maciejmatczak/more-organic/data/case/assembly.scad

$fa = 6;
$fs = .1;


union() {
	color(c = [1, 1, 0.8000000000, 0.5000000000]) {
		linear_extrude(height = 1.6000000000) {
			offset(r = -2) {
				offset(r = 2) {
					union() {
						offset(r = -12) {
							offset(r = 16) {
								union() {
									intersection() {
										offset(r = -10) {
											offset(r = 10) {
												translate(v = [-16.2000000000, -42.8000000000]) {
													rotate(a = 180.0000000000) {
														polygon(paths = [[0, 1, 2, 3]], points = [[-1.5000000000, 1.5000000000], [8, 1.5000000000], [8, -6], [-1.5000000000, -6]]);
													}
												}
												translate(v = [-40.0000000000, -2.0000000000]) {
													color(c = [0.3000000000, 0.3000000000, 0.3000000000]) {
														mirror(v = [0, 1, 0]) {
															polygon(paths = [[0, 1, 2, 3, 4, 5, 6, 7]], points = [[-5.3500000000, 12.1000000000], [5.3500000000, 12.1000000000], [5.3500000000, 0], [5.1000000000, 0], [5.1000000000, -2], [-5.1000000000, -2], [-5.1000000000, 0], [-5.3500000000, 0]]);
														}
													}
												}
												translate(v = [-24.0000000000, -17.8000000000]) {
													rotate(a = -90.0000000000) {
														color(c = [0.0040000000, 0.2274509804, 0.5764705882, 0.5000000000]) {
															polygon(paths = [[0, 1, 2, 3]], points = [[-17.8000000000, 8.9000000000], [15.2000000000, 8.9000000000], [15.2000000000, -8.9000000000], [-17.8000000000, -8.9000000000]]);
														}
													}
												}
												translate(v = [-39.8000000000, -21.2000000000]) {
													rotate(a = -90.0000000000) {
														polygon(paths = [[0, 1, 2, 3]], points = [[-4.7000000000, -1.1000000000], [4.7000000000, -1.1000000000], [4.7000000000, 1.1000000000], [-4.7000000000, 1.1000000000]]);
													}
												}
												translate(v = [-43.3000000000, -21.2000000000]) {
													rotate(a = -90.0000000000) {
														polygon(paths = [[0, 1, 2, 3]], points = [[-4.7000000000, -1.1000000000], [4.7000000000, -1.1000000000], [4.7000000000, 1.1000000000], [-4.7000000000, 1.1000000000]]);
													}
												}
												translate(v = [-36.1000000000, -18.6000000000]) {
													rotate(a = 180.0000000000) {
														polygon(paths = [[0, 1, 2, 3]], points = [[-1.6500000000, -1.2400000000], [1.6500000000, -1.2400000000], [1.6500000000, 1.2400000000], [-1.6500000000, 1.2400000000]]);
													}
												}
												translate(v = [-36.1000000000, -24.4000000000]) {
													polygon(paths = [[0, 1, 2, 3]], points = [[-1.6500000000, -1.2400000000], [1.6500000000, -1.2400000000], [1.6500000000, 1.2400000000], [-1.6500000000, 1.2400000000]]);
												}
											}
										}
										translate(v = [0, -4]) {
											offset(r = -10) {
												offset(r = 10) {
													translate(v = [-16.2000000000, -42.8000000000]) {
														rotate(a = 180.0000000000) {
															polygon(paths = [[0, 1, 2, 3]], points = [[-1.5000000000, 1.5000000000], [8, 1.5000000000], [8, -6], [-1.5000000000, -6]]);
														}
													}
													translate(v = [-40.0000000000, -2.0000000000]) {
														color(c = [0.3000000000, 0.3000000000, 0.3000000000]) {
															mirror(v = [0, 1, 0]) {
																polygon(paths = [[0, 1, 2, 3, 4, 5, 6, 7]], points = [[-5.3500000000, 12.1000000000], [5.3500000000, 12.1000000000], [5.3500000000, 0], [5.1000000000, 0], [5.1000000000, -2], [-5.1000000000, -2], [-5.1000000000, 0], [-5.3500000000, 0]]);
															}
														}
													}
													translate(v = [-24.0000000000, -17.8000000000]) {
														rotate(a = -90.0000000000) {
															color(c = [0.0040000000, 0.2274509804, 0.5764705882, 0.5000000000]) {
																polygon(paths = [[0, 1, 2, 3]], points = [[-17.8000000000, 8.9000000000], [15.2000000000, 8.9000000000], [15.2000000000, -8.9000000000], [-17.8000000000, -8.9000000000]]);
															}
														}
													}
													translate(v = [-39.8000000000, -21.2000000000]) {
														rotate(a = -90.0000000000) {
															polygon(paths = [[0, 1, 2, 3]], points = [[-4.7000000000, -1.1000000000], [4.7000000000, -1.1000000000], [4.7000000000, 1.1000000000], [-4.7000000000, 1.1000000000]]);
														}
													}
													translate(v = [-43.3000000000, -21.2000000000]) {
														rotate(a = -90.0000000000) {
															polygon(paths = [[0, 1, 2, 3]], points = [[-4.7000000000, -1.1000000000], [4.7000000000, -1.1000000000], [4.7000000000, 1.1000000000], [-4.7000000000, 1.1000000000]]);
														}
													}
													translate(v = [-36.1000000000, -18.6000000000]) {
														rotate(a = 180.0000000000) {
															polygon(paths = [[0, 1, 2, 3]], points = [[-1.6500000000, -1.2400000000], [1.6500000000, -1.2400000000], [1.6500000000, 1.2400000000], [-1.6500000000, 1.2400000000]]);
														}
													}
													translate(v = [-36.1000000000, -24.4000000000]) {
														polygon(paths = [[0, 1, 2, 3]], points = [[-1.6500000000, -1.2400000000], [1.6500000000, -1.2400000000], [1.6500000000, 1.2400000000], [-1.6500000000, 1.2400000000]]);
													}
												}
											}
										}
									}
									translate(v = [13.4000000000, -78.5000000000]) {
										rotate(a = -6.6000000000) {
											translate(v = [-7.8000000000, -7.0000000000]) {
												polygon(paths = [[0, 1, 2, 3, 4, 5, 6, 7, 8, 9, 10, 11, 12, 13, 14, 15, 16, 17, 18, 19]], points = [[0.8000000000, 0], [14.8000000000, 0], [14.8000000000, 1], [15.6000000000, 1], [15.6000000000, 4.5000000000], [14.8000000000, 4.5000000000], [14.8000000000, 9.5000000000], [15.6000000000, 9.5000000000], [15.6000000000, 13], [14.8000000000, 13], [14.8000000000, 14], [0.8000000000, 14], [0.8000000000, 13], [0, 13], [0, 9.5000000000], [0.8000000000, 9.5000000000], [0.8000000000, 4.5000000000], [0, 4.5000000000], [0, 1], [0.8000000000, 1]]);
											}
										}
									}
									translate(v = [-9.3000000000, -79.9000000000]) {
										rotate(a = 18.0000000000) {
											translate(v = [-7.8000000000, -7.0000000000]) {
												polygon(paths = [[0, 1, 2, 3, 4, 5, 6, 7, 8, 9, 10, 11, 12, 13, 14, 15, 16, 17, 18, 19]], points = [[0.8000000000, 0], [14.8000000000, 0], [14.8000000000, 1], [15.6000000000, 1], [15.6000000000, 4.5000000000], [14.8000000000, 4.5000000000], [14.8000000000, 9.5000000000], [15.6000000000, 9.5000000000], [15.6000000000, 13], [14.8000000000, 13], [14.8000000000, 14], [0.8000000000, 14], [0.8000000000, 13], [0, 13], [0, 9.5000000000], [0.8000000000, 9.5000000000], [0.8000000000, 4.5000000000], [0, 4.5000000000], [0, 1], [0.8000000000, 1]]);
											}
										}
									}
									translate(v = [-28.0000000000, -91.2000000000]) {
										rotate(a = 35.0000000000) {
											translate(v = [-7.8000000000, -7.0000000000]) {
												polygon(paths = [[0, 1, 2, 3, 4, 5, 6, 7, 8, 9, 10, 11, 12, 13, 14, 15, 16, 17, 18, 19]], points = [[0.8000000000, 0], [14.8000000000, 0], [14.8000000000, 1], [15.6000000000, 1], [15.6000000000, 4.5000000000], [14.8000000000, 4.5000000000], [14.8000000000, 9.5000000000], [15.6000000000, 9.5000000000], [15.6000000000, 13], [14.8000000000, 13], [14.8000000000, 14], [0.8000000000, 14], [0.8000000000, 13], [0, 13], [0, 9.5000000000], [0.8000000000, 9.5000000000], [0.8000000000, 4.5000000000], [0, 4.5000000000], [0, 1], [0.8000000000, 1]]);
											}
										}
									}
									translate(v = [95.2500000000, -62.1500000000]) {
										translate(v = [-7.8000000000, -7.0000000000]) {
											polygon(paths = [[0, 1, 2, 3, 4, 5, 6, 7, 8, 9, 10, 11, 12, 13, 14, 15, 16, 17, 18, 19]], points = [[0.8000000000, 0], [14.8000000000, 0], [14.8000000000, 1], [15.6000000000, 1], [15.6000000000, 4.5000000000], [14.8000000000, 4.5000000000], [14.8000000000, 9.5000000000], [15.6000000000, 9.5000000000], [15.6000000000, 13], [14.8000000000, 13], [14.8000000000, 14], [0.8000000000, 14], [0.8000000000, 13], [0, 13], [0, 9.5000000000], [0.8000000000, 9.5000000000], [0.8000000000, 4.5000000000], [0, 4.5000000000], [0, 1], [0.8000000000, 1]]);
										}
									}
									translate(v = [76.2000000000, -61.1500000000]) {
										translate(v = [-7.8000000000, -7.0000000000]) {
											polygon(paths = [[0, 1, 2, 3, 4, 5, 6, 7, 8, 9, 10, 11, 12, 13, 14, 15, 16, 17, 18, 19]], points = [[0.8000000000, 0], [14.8000000000, 0], [14.8000000000, 1], [15.6000000000, 1], [15.6000000000, 4.5000000000], [14.8000000000, 4.5000000000], [14.8000000000, 9.5000000000], [15.6000000000, 9.5000000000], [15.6000000000, 13], [14.8000000000, 13], [14.8000000000, 14], [0.8000000000, 14], [0.8000000000, 13], [0, 13], [0, 9.5000000000], [0.8000000000, 9.5000000000], [0.8000000000, 4.5000000000], [0, 4.5000000000], [0, 1], [0.8000000000, 1]]);
										}
									}
									translate(v = [57.1500000000, -56.1500000000]) {
										translate(v = [-7.8000000000, -7.0000000000]) {
											polygon(paths = [[0, 1, 2, 3, 4, 5, 6, 7, 8, 9, 10, 11, 12, 13, 14, 15, 16, 17, 18, 19]], points = [[0.8000000000, 0], [14.8000000000, 0], [14.8000000000, 1], [15.6000000000, 1], [15.6000000000, 4.5000000000], [14.8000000000, 4.5000000000], [14.8000000000, 9.5000000000], [15.6000000000, 9.5000000000], [15.6000000000, 13], [14.8000000000, 13], [14.8000000000, 14], [0.8000000000, 14], [0.8000000000, 13], [0, 13], [0, 9.5000000000], [0.8000000000, 9.5000000000], [0.8000000000, 4.5000000000], [0, 4.5000000000], [0, 1], [0.8000000000, 1]]);
										}
									}
									translate(v = [38.1000000000, -52.1500000000]) {
										translate(v = [-7.8000000000, -7.0000000000]) {
											polygon(paths = [[0, 1, 2, 3, 4, 5, 6, 7, 8, 9, 10, 11, 12, 13, 14, 15, 16, 17, 18, 19]], points = [[0.8000000000, 0], [14.8000000000, 0], [14.8000000000, 1], [15.6000000000, 1], [15.6000000000, 4.5000000000], [14.8000000000, 4.5000000000], [14.8000000000, 9.5000000000], [15.6000000000, 9.5000000000], [15.6000000000, 13], [14.8000000000, 13], [14.8000000000, 14], [0.8000000000, 14], [0.8000000000, 13], [0, 13], [0, 9.5000000000], [0.8000000000, 9.5000000000], [0.8000000000, 4.5000000000], [0, 4.5000000000], [0, 1], [0.8000000000, 1]]);
										}
									}
									translate(v = [19.0500000000, -57.1500000000]) {
										translate(v = [-7.8000000000, -7.0000000000]) {
											polygon(paths = [[0, 1, 2, 3, 4, 5, 6, 7, 8, 9, 10, 11, 12, 13, 14, 15, 16, 17, 18, 19]], points = [[0.8000000000, 0], [14.8000000000, 0], [14.8000000000, 1], [15.6000000000, 1], [15.6000000000, 4.5000000000], [14.8000000000, 4.5000000000], [14.8000000000, 9.5000000000], [15.6000000000, 9.5000000000], [15.6000000000, 13], [14.8000000000, 13], [14.8000000000, 14], [0.8000000000, 14], [0.8000000000, 13], [0, 13], [0, 9.5000000000], [0.8000000000, 9.5000000000], [0.8000000000, 4.5000000000], [0, 4.5000000000], [0, 1], [0.8000000000, 1]]);
										}
									}
									translate(v = [0.0000000000, -58.1500000000]) {
										translate(v = [-7.8000000000, -7.0000000000]) {
											polygon(paths = [[0, 1, 2, 3, 4, 5, 6, 7, 8, 9, 10, 11, 12, 13, 14, 15, 16, 17, 18, 19]], points = [[0.8000000000, 0], [14.8000000000, 0], [14.8000000000, 1], [15.6000000000, 1], [15.6000000000, 4.5000000000], [14.8000000000, 4.5000000000], [14.8000000000, 9.5000000000], [15.6000000000, 9.5000000000], [15.6000000000, 13], [14.8000000000, 13], [14.8000000000, 14], [0.8000000000, 14], [0.8000000000, 13], [0, 13], [0, 9.5000000000], [0.8000000000, 9.5000000000], [0.8000000000, 4.5000000000], [0, 4.5000000000], [0, 1], [0.8000000000, 1]]);
										}
									}
									translate(v = [95.2500000000, -43.1000000000]) {
										translate(v = [-7.8000000000, -7.0000000000]) {
											polygon(paths = [[0, 1, 2, 3, 4, 5, 6, 7, 8, 9, 10, 11, 12, 13, 14, 15, 16, 17, 18, 19]], points = [[0.8000000000, 0], [14.8000000000, 0], [14.8000000000, 1], [15.6000000000, 1], [15.6000000000, 4.5000000000], [14.8000000000, 4.5000000000], [14.8000000000, 9.5000000000], [15.6000000000, 9.5000000000], [15.6000000000, 13], [14.8000000000, 13], [14.8000000000, 14], [0.8000000000, 14], [0.8000000000, 13], [0, 13], [0, 9.5000000000], [0.8000000000, 9.5000000000], [0.8000000000, 4.5000000000], [0, 4.5000000000], [0, 1], [0.8000000000, 1]]);
										}
									}
									translate(v = [76.2000000000, -42.1000000000]) {
										translate(v = [-7.8000000000, -7.0000000000]) {
											polygon(paths = [[0, 1, 2, 3, 4, 5, 6, 7, 8, 9, 10, 11, 12, 13, 14, 15, 16, 17, 18, 19]], points = [[0.8000000000, 0], [14.8000000000, 0], [14.8000000000, 1], [15.6000000000, 1], [15.6000000000, 4.5000000000], [14.8000000000, 4.5000000000], [14.8000000000, 9.5000000000], [15.6000000000, 9.5000000000], [15.6000000000, 13], [14.8000000000, 13], [14.8000000000, 14], [0.8000000000, 14], [0.8000000000, 13], [0, 13], [0, 9.5000000000], [0.8000000000, 9.5000000000], [0.8000000000, 4.5000000000], [0, 4.5000000000], [0, 1], [0.8000000000, 1]]);
										}
									}
									translate(v = [57.1500000000, -37.1000000000]) {
										translate(v = [-7.8000000000, -7.0000000000]) {
											polygon(paths = [[0, 1, 2, 3, 4, 5, 6, 7, 8, 9, 10, 11, 12, 13, 14, 15, 16, 17, 18, 19]], points = [[0.8000000000, 0], [14.8000000000, 0], [14.8000000000, 1], [15.6000000000, 1], [15.6000000000, 4.5000000000], [14.8000000000, 4.5000000000], [14.8000000000, 9.5000000000], [15.6000000000, 9.5000000000], [15.6000000000, 13], [14.8000000000, 13], [14.8000000000, 14], [0.8000000000, 14], [0.8000000000, 13], [0, 13], [0, 9.5000000000], [0.8000000000, 9.5000000000], [0.8000000000, 4.5000000000], [0, 4.5000000000], [0, 1], [0.8000000000, 1]]);
										}
									}
									translate(v = [38.1000000000, -33.1000000000]) {
										translate(v = [-7.8000000000, -7.0000000000]) {
											polygon(paths = [[0, 1, 2, 3, 4, 5, 6, 7, 8, 9, 10, 11, 12, 13, 14, 15, 16, 17, 18, 19]], points = [[0.8000000000, 0], [14.8000000000, 0], [14.8000000000, 1], [15.6000000000, 1], [15.6000000000, 4.5000000000], [14.8000000000, 4.5000000000], [14.8000000000, 9.5000000000], [15.6000000000, 9.5000000000], [15.6000000000, 13], [14.8000000000, 13], [14.8000000000, 14], [0.8000000000, 14], [0.8000000000, 13], [0, 13], [0, 9.5000000000], [0.8000000000, 9.5000000000], [0.8000000000, 4.5000000000], [0, 4.5000000000], [0, 1], [0.8000000000, 1]]);
										}
									}
									translate(v = [19.0500000000, -38.1000000000]) {
										translate(v = [-7.8000000000, -7.0000000000]) {
											polygon(paths = [[0, 1, 2, 3, 4, 5, 6, 7, 8, 9, 10, 11, 12, 13, 14, 15, 16, 17, 18, 19]], points = [[0.8000000000, 0], [14.8000000000, 0], [14.8000000000, 1], [15.6000000000, 1], [15.6000000000, 4.5000000000], [14.8000000000, 4.5000000000], [14.8000000000, 9.5000000000], [15.6000000000, 9.5000000000], [15.6000000000, 13], [14.8000000000, 13], [14.8000000000, 14], [0.8000000000, 14], [0.8000000000, 13], [0, 13], [0, 9.5000000000], [0.8000000000, 9.5000000000], [0.8000000000, 4.5000000000], [0, 4.5000000000], [0, 1], [0.8000000000, 1]]);
										}
									}
									translate(v = [0.0000000000, -39.1000000000]) {
										translate(v = [-7.8000000000, -7.0000000000]) {
											polygon(paths = [[0, 1, 2, 3, 4, 5, 6, 7, 8, 9, 10, 11, 12, 13, 14, 15, 16, 17, 18, 19]], points = [[0.8000000000, 0], [14.8000000000, 0], [14.8000000000, 1], [15.6000000000, 1], [15.6000000000, 4.5000000000], [14.8000000000, 4.5000000000], [14.8000000000, 9.5000000000], [15.6000000000, 9.5000000000], [15.6000000000, 13], [14.8000000000, 13], [14.8000000000, 14], [0.8000000000, 14], [0.8000000000, 13], [0, 13], [0, 9.5000000000], [0.8000000000, 9.5000000000], [0.8000000000, 4.5000000000], [0, 4.5000000000], [0, 1], [0.8000000000, 1]]);
										}
									}
									translate(v = [95.2500000000, -24.0500000000]) {
										translate(v = [-7.8000000000, -7.0000000000]) {
											polygon(paths = [[0, 1, 2, 3, 4, 5, 6, 7, 8, 9, 10, 11, 12, 13, 14, 15, 16, 17, 18, 19]], points = [[0.8000000000, 0], [14.8000000000, 0], [14.8000000000, 1], [15.6000000000, 1], [15.6000000000, 4.5000000000], [14.8000000000, 4.5000000000], [14.8000000000, 9.5000000000], [15.6000000000, 9.5000000000], [15.6000000000, 13], [14.8000000000, 13], [14.8000000000, 14], [0.8000000000, 14], [0.8000000000, 13], [0, 13], [0, 9.5000000000], [0.8000000000, 9.5000000000], [0.8000000000, 4.5000000000], [0, 4.5000000000], [0, 1], [0.8000000000, 1]]);
										}
									}
									translate(v = [76.2000000000, -23.0500000000]) {
										translate(v = [-7.8000000000, -7.0000000000]) {
											polygon(paths = [[0, 1, 2, 3, 4, 5, 6, 7, 8, 9, 10, 11, 12, 13, 14, 15, 16, 17, 18, 19]], points = [[0.8000000000, 0], [14.8000000000, 0], [14.8000000000, 1], [15.6000000000, 1], [15.6000000000, 4.5000000000], [14.8000000000, 4.5000000000], [14.8000000000, 9.5000000000], [15.6000000000, 9.5000000000], [15.6000000000, 13], [14.8000000000, 13], [14.8000000000, 14], [0.8000000000, 14], [0.8000000000, 13], [0, 13], [0, 9.5000000000], [0.8000000000, 9.5000000000], [0.8000000000, 4.5000000000], [0, 4.5000000000], [0, 1], [0.8000000000, 1]]);
										}
									}
									translate(v = [57.1500000000, -18.0500000000]) {
										translate(v = [-7.8000000000, -7.0000000000]) {
											polygon(paths = [[0, 1, 2, 3, 4, 5, 6, 7, 8, 9, 10, 11, 12, 13, 14, 15, 16, 17, 18, 19]], points = [[0.8000000000, 0], [14.8000000000, 0], [14.8000000000, 1], [15.6000000000, 1], [15.6000000000, 4.5000000000], [14.8000000000, 4.5000000000], [14.8000000000, 9.5000000000], [15.6000000000, 9.5000000000], [15.6000000000, 13], [14.8000000000, 13], [14.8000000000, 14], [0.8000000000, 14], [0.8000000000, 13], [0, 13], [0, 9.5000000000], [0.8000000000, 9.5000000000], [0.8000000000, 4.5000000000], [0, 4.5000000000], [0, 1], [0.8000000000, 1]]);
										}
									}
									translate(v = [38.1000000000, -14.0500000000]) {
										translate(v = [-7.8000000000, -7.0000000000]) {
											polygon(paths = [[0, 1, 2, 3, 4, 5, 6, 7, 8, 9, 10, 11, 12, 13, 14, 15, 16, 17, 18, 19]], points = [[0.8000000000, 0], [14.8000000000, 0], [14.8000000000, 1], [15.6000000000, 1], [15.6000000000, 4.5000000000], [14.8000000000, 4.5000000000], [14.8000000000, 9.5000000000], [15.6000000000, 9.5000000000], [15.6000000000, 13], [14.8000000000, 13], [14.8000000000, 14], [0.8000000000, 14], [0.8000000000, 13], [0, 13], [0, 9.5000000000], [0.8000000000, 9.5000000000], [0.8000000000, 4.5000000000], [0, 4.5000000000], [0, 1], [0.8000000000, 1]]);
										}
									}
									translate(v = [19.0500000000, -19.0500000000]) {
										translate(v = [-7.8000000000, -7.0000000000]) {
											polygon(paths = [[0, 1, 2, 3, 4, 5, 6, 7, 8, 9, 10, 11, 12, 13, 14, 15, 16, 17, 18, 19]], points = [[0.8000000000, 0], [14.8000000000, 0], [14.8000000000, 1], [15.6000000000, 1], [15.6000000000, 4.5000000000], [14.8000000000, 4.5000000000], [14.8000000000, 9.5000000000], [15.6000000000, 9.5000000000], [15.6000000000, 13], [14.8000000000, 13], [14.8000000000, 14], [0.8000000000, 14], [0.8000000000, 13], [0, 13], [0, 9.5000000000], [0.8000000000, 9.5000000000], [0.8000000000, 4.5000000000], [0, 4.5000000000], [0, 1], [0.8000000000, 1]]);
										}
									}
									translate(v = [0.0000000000, -20.0500000000]) {
										translate(v = [-7.8000000000, -7.0000000000]) {
											polygon(paths = [[0, 1, 2, 3, 4, 5, 6, 7, 8, 9, 10, 11, 12, 13, 14, 15, 16, 17, 18, 19]], points = [[0.8000000000, 0], [14.8000000000, 0], [14.8000000000, 1], [15.6000000000, 1], [15.6000000000, 4.5000000000], [14.8000000000, 4.5000000000], [14.8000000000, 9.5000000000], [15.6000000000, 9.5000000000], [15.6000000000, 13], [14.8000000000, 13], [14.8000000000, 14], [0.8000000000, 14], [0.8000000000, 13], [0, 13], [0, 9.5000000000], [0.8000000000, 9.5000000000], [0.8000000000, 4.5000000000], [0, 4.5000000000], [0, 1], [0.8000000000, 1]]);
										}
									}
									translate(v = [95.2500000000, -5.0000000000]) {
										translate(v = [-7.8000000000, -7.0000000000]) {
											polygon(paths = [[0, 1, 2, 3, 4, 5, 6, 7, 8, 9, 10, 11, 12, 13, 14, 15, 16, 17, 18, 19]], points = [[0.8000000000, 0], [14.8000000000, 0], [14.8000000000, 1], [15.6000000000, 1], [15.6000000000, 4.5000000000], [14.8000000000, 4.5000000000], [14.8000000000, 9.5000000000], [15.6000000000, 9.5000000000], [15.6000000000, 13], [14.8000000000, 13], [14.8000000000, 14], [0.8000000000, 14], [0.8000000000, 13], [0, 13], [0, 9.5000000000], [0.8000000000, 9.5000000000], [0.8000000000, 4.5000000000], [0, 4.5000000000], [0, 1], [0.8000000000, 1]]);
										}
									}
									translate(v = [76.2000000000, -4.0000000000]) {
										translate(v = [-7.8000000000, -7.0000000000]) {
											polygon(paths = [[0, 1, 2, 3, 4, 5, 6, 7, 8, 9, 10, 11, 12, 13, 14, 15, 16, 17, 18, 19]], points = [[0.8000000000, 0], [14.8000000000, 0], [14.8000000000, 1], [15.6000000000, 1], [15.6000000000, 4.5000000000], [14.8000000000, 4.5000000000], [14.8000000000, 9.5000000000], [15.6000000000, 9.5000000000], [15.6000000000, 13], [14.8000000000, 13], [14.8000000000, 14], [0.8000000000, 14], [0.8000000000, 13], [0, 13], [0, 9.5000000000], [0.8000000000, 9.5000000000], [0.8000000000, 4.5000000000], [0, 4.5000000000], [0, 1], [0.8000000000, 1]]);
										}
									}
									translate(v = [57.1500000000, 1.0000000000]) {
										translate(v = [-7.8000000000, -7.0000000000]) {
											polygon(paths = [[0, 1, 2, 3, 4, 5, 6, 7, 8, 9, 10, 11, 12, 13, 14, 15, 16, 17, 18, 19]], points = [[0.8000000000, 0], [14.8000000000, 0], [14.8000000000, 1], [15.6000000000, 1], [15.6000000000, 4.5000000000], [14.8000000000, 4.5000000000], [14.8000000000, 9.5000000000], [15.6000000000, 9.5000000000], [15.6000000000, 13], [14.8000000000, 13], [14.8000000000, 14], [0.8000000000, 14], [0.8000000000, 13], [0, 13], [0, 9.5000000000], [0.8000000000, 9.5000000000], [0.8000000000, 4.5000000000], [0, 4.5000000000], [0, 1], [0.8000000000, 1]]);
										}
									}
									translate(v = [38.1000000000, 5.0000000000]) {
										translate(v = [-7.8000000000, -7.0000000000]) {
											polygon(paths = [[0, 1, 2, 3, 4, 5, 6, 7, 8, 9, 10, 11, 12, 13, 14, 15, 16, 17, 18, 19]], points = [[0.8000000000, 0], [14.8000000000, 0], [14.8000000000, 1], [15.6000000000, 1], [15.6000000000, 4.5000000000], [14.8000000000, 4.5000000000], [14.8000000000, 9.5000000000], [15.6000000000, 9.5000000000], [15.6000000000, 13], [14.8000000000, 13], [14.8000000000, 14], [0.8000000000, 14], [0.8000000000, 13], [0, 13], [0, 9.5000000000], [0.8000000000, 9.5000000000], [0.8000000000, 4.5000000000], [0, 4.5000000000], [0, 1], [0.8000000000, 1]]);
										}
									}
									translate(v = [19.0500000000, -0.0000000000]) {
										translate(v = [-7.8000000000, -7.0000000000]) {
											polygon(paths = [[0, 1, 2, 3, 4, 5, 6, 7, 8, 9, 10, 11, 12, 13, 14, 15, 16, 17, 18, 19]], points = [[0.8000000000, 0], [14.8000000000, 0], [14.8000000000, 1], [15.6000000000, 1], [15.6000000000, 4.5000000000], [14.8000000000, 4.5000000000], [14.8000000000, 9.5000000000], [15.6000000000, 9.5000000000], [15.6000000000, 13], [14.8000000000, 13], [14.8000000000, 14], [0.8000000000, 14], [0.8000000000, 13], [0, 13], [0, 9.5000000000], [0.8000000000, 9.5000000000], [0.8000000000, 4.5000000000], [0, 4.5000000000], [0, 1], [0.8000000000, 1]]);
										}
									}
									translate(v = [0.0000000000, -1.0000000000]) {
										translate(v = [-7.8000000000, -7.0000000000]) {
											polygon(paths = [[0, 1, 2, 3, 4, 5, 6, 7, 8, 9, 10, 11, 12, 13, 14, 15, 16, 17, 18, 19]], points = [[0.8000000000, 0], [14.8000000000, 0], [14.8000000000, 1], [15.6000000000, 1], [15.6000000000, 4.5000000000], [14.8000000000, 4.5000000000], [14.8000000000, 9.5000000000], [15.6000000000, 9.5000000000], [15.6000000000, 13], [14.8000000000, 13], [14.8000000000, 14], [0.8000000000, 14], [0.8000000000, 13], [0, 13], [0, 9.5000000000], [0.8000000000, 9.5000000000], [0.8000000000, 4.5000000000], [0, 4.5000000000], [0, 1], [0.8000000000, 1]]);
										}
									}
								}
							}
						}
						offset(r = 2) {
							union() {
								translate(v = [63.6750000000, -68.6750000000]) {
									circle(r = 1.2500000000);
								}
								translate(v = [69.6750000000, 8.5250000000]) {
									circle(r = 1.2500000000);
								}
								translate(v = [25.5750000000, 12.5250000000]) {
									circle(r = 1.2500000000);
								}
								translate(v = [-31.0000000000, -39.0000000000]) {
									circle(r = 1.2500000000);
								}
								translate(v = [-18.0000000000, -48.0000000000]) {
									circle(r = 1.2500000000);
								}
								translate(v = [-44.0000000000, -30.0000000000]) {
									circle(r = 1.2500000000);
								}
							}
						}
					}
				}
			}
		}
	}
	translate(v = [0, 0, 1.7000000000]) {
		linear_extrude(height = 2) {
			translate(v = [-16.2000000000, -42.8000000000]) {
				rotate(a = 180.0000000000) {
					polygon(paths = [[0, 1, 2, 3]], points = [[-1.5000000000, 1.5000000000], [8, 1.5000000000], [8, -6], [-1.5000000000, -6]]);
				}
			}
			translate(v = [-40.0000000000, -2.0000000000]) {
				color(c = [0.3000000000, 0.3000000000, 0.3000000000]) {
					mirror(v = [0, 1, 0]) {
						polygon(paths = [[0, 1, 2, 3, 4, 5, 6, 7]], points = [[-5.3500000000, 12.1000000000], [5.3500000000, 12.1000000000], [5.3500000000, 0], [5.1000000000, 0], [5.1000000000, -2], [-5.1000000000, -2], [-5.1000000000, 0], [-5.3500000000, 0]]);
					}
				}
			}
			translate(v = [-24.0000000000, -17.8000000000]) {
				rotate(a = -90.0000000000) {
					color(c = [0.0040000000, 0.2274509804, 0.5764705882, 0.5000000000]) {
						polygon(paths = [[0, 1, 2, 3]], points = [[-17.8000000000, 8.9000000000], [15.2000000000, 8.9000000000], [15.2000000000, -8.9000000000], [-17.8000000000, -8.9000000000]]);
					}
				}
			}
			translate(v = [-39.8000000000, -21.2000000000]) {
				rotate(a = -90.0000000000) {
					polygon(paths = [[0, 1, 2, 3]], points = [[-4.7000000000, -1.1000000000], [4.7000000000, -1.1000000000], [4.7000000000, 1.1000000000], [-4.7000000000, 1.1000000000]]);
				}
			}
			translate(v = [-43.3000000000, -21.2000000000]) {
				rotate(a = -90.0000000000) {
					polygon(paths = [[0, 1, 2, 3]], points = [[-4.7000000000, -1.1000000000], [4.7000000000, -1.1000000000], [4.7000000000, 1.1000000000], [-4.7000000000, 1.1000000000]]);
				}
			}
			translate(v = [-36.1000000000, -18.6000000000]) {
				rotate(a = 180.0000000000) {
					polygon(paths = [[0, 1, 2, 3]], points = [[-1.6500000000, -1.2400000000], [1.6500000000, -1.2400000000], [1.6500000000, 1.2400000000], [-1.6500000000, 1.2400000000]]);
				}
			}
			translate(v = [-36.1000000000, -24.4000000000]) {
				polygon(paths = [[0, 1, 2, 3]], points = [[-1.6500000000, -1.2400000000], [1.6500000000, -1.2400000000], [1.6500000000, 1.2400000000], [-1.6500000000, 1.2400000000]]);
			}
		}
	}
	color(c = [0.3000000000, 0.3000000000, 0.3000000000, 0.4000000000]) {
		translate(v = [0, 0, 6.6010000000]) {
			union() {
				translate(v = [0, 12]) {
					union() {
						translate(v = [0, 0, 1.5000000000]) {
							cylinder(center = true, h = 3, r = 4);
						}
						translate(v = [0, 0, -4]) {
							cylinder(center = true, h = 8, r = 2);
						}
					}
				}
				translate(v = [0, -94]) {
					union() {
						translate(v = [0, 0, 1.5000000000]) {
							cylinder(center = true, h = 3, r = 4);
						}
						translate(v = [0, 0, -4]) {
							cylinder(center = true, h = 8, r = 2);
						}
					}
				}
				translate(v = [81.7250000000, 12]) {
					union() {
						translate(v = [0, 0, 1.5000000000]) {
							cylinder(center = true, h = 3, r = 4);
						}
						translate(v = [0, 0, -4]) {
							cylinder(center = true, h = 8, r = 2);
						}
					}
				}
				translate(v = [81.7250000000, -94]) {
					union() {
						translate(v = [0, 0, 1.5000000000]) {
							cylinder(center = true, h = 3, r = 4);
						}
						translate(v = [0, 0, -4]) {
							cylinder(center = true, h = 8, r = 2);
						}
					}
				}
			}
		}
	}
	color(c = [0.3000000000, 0.3000000000, 0.3000000000, 0.4000000000]) {
		translate(v = [0, 0, 6.6010000000]) {
			union() {
				translate(v = [63.6750000000, -68.6750000000]) {
					union() {
						translate(v = [0, 0, 1]) {
							cylinder(center = true, h = 2, r = 2);
						}
						translate(v = [0, 0, -4]) {
							cylinder(center = true, h = 8, r = 1);
						}
					}
				}
				translate(v = [69.6750000000, 8.5250000000]) {
					union() {
						translate(v = [0, 0, 1]) {
							cylinder(center = true, h = 2, r = 2);
						}
						translate(v = [0, 0, -4]) {
							cylinder(center = true, h = 8, r = 1);
						}
					}
				}
				translate(v = [25.5750000000, 12.5250000000]) {
					union() {
						translate(v = [0, 0, 1]) {
							cylinder(center = true, h = 2, r = 2);
						}
						translate(v = [0, 0, -4]) {
							cylinder(center = true, h = 8, r = 1);
						}
					}
				}
				translate(v = [-31.0000000000, -39.0000000000]) {
					union() {
						translate(v = [0, 0, 1]) {
							cylinder(center = true, h = 2, r = 2);
						}
						translate(v = [0, 0, -4]) {
							cylinder(center = true, h = 8, r = 1);
						}
					}
				}
				translate(v = [-18.0000000000, -48.0000000000]) {
					union() {
						translate(v = [0, 0, 1]) {
							cylinder(center = true, h = 2, r = 2);
						}
						translate(v = [0, 0, -4]) {
							cylinder(center = true, h = 8, r = 1);
						}
					}
				}
				translate(v = [-44.0000000000, -30.0000000000]) {
					union() {
						translate(v = [0, 0, 1]) {
							cylinder(center = true, h = 2, r = 2);
						}
						translate(v = [0, 0, -4]) {
							cylinder(center = true, h = 8, r = 1);
						}
					}
				}
			}
		}
	}
	translate(v = [0, 0, 5]) {
		color(c = [0.8000000000, 0.8500000000, 1, 0.5000000000]) {
			linear_extrude(height = 1.6000000000) {
				difference() {
					offset(r = -20) {
						offset(r = 20) {
							union() {
								offset(r = -13) {
									offset(r = 16) {
										translate(v = [13.4000000000, -78.5000000000]) {
											rotate(a = -6.6000000000) {
												square(center = true, size = [19.0500000000, 19.0500000000]);
											}
										}
										translate(v = [-9.3000000000, -79.9000000000]) {
											rotate(a = 18.0000000000) {
												square(center = true, size = [19.0500000000, 19.0500000000]);
											}
										}
										translate(v = [-28.0000000000, -91.2000000000]) {
											rotate(a = 35.0000000000) {
												square(center = true, size = [19.0500000000, 19.0500000000]);
											}
										}
										translate(v = [95.2500000000, -62.1500000000]) {
											square(center = true, size = [19.0500000000, 19.0500000000]);
										}
										translate(v = [76.2000000000, -61.1500000000]) {
											square(center = true, size = [19.0500000000, 19.0500000000]);
										}
										translate(v = [57.1500000000, -56.1500000000]) {
											square(center = true, size = [19.0500000000, 19.0500000000]);
										}
										translate(v = [38.1000000000, -52.1500000000]) {
											square(center = true, size = [19.0500000000, 19.0500000000]);
										}
										translate(v = [19.0500000000, -57.1500000000]) {
											square(center = true, size = [19.0500000000, 19.0500000000]);
										}
										translate(v = [0.0000000000, -58.1500000000]) {
											square(center = true, size = [19.0500000000, 19.0500000000]);
										}
										translate(v = [95.2500000000, -43.1000000000]) {
											square(center = true, size = [19.0500000000, 19.0500000000]);
										}
										translate(v = [76.2000000000, -42.1000000000]) {
											square(center = true, size = [19.0500000000, 19.0500000000]);
										}
										translate(v = [57.1500000000, -37.1000000000]) {
											square(center = true, size = [19.0500000000, 19.0500000000]);
										}
										translate(v = [38.1000000000, -33.1000000000]) {
											square(center = true, size = [19.0500000000, 19.0500000000]);
										}
										translate(v = [19.0500000000, -38.1000000000]) {
											square(center = true, size = [19.0500000000, 19.0500000000]);
										}
										translate(v = [0.0000000000, -39.1000000000]) {
											square(center = true, size = [19.0500000000, 19.0500000000]);
										}
										translate(v = [95.2500000000, -24.0500000000]) {
											square(center = true, size = [19.0500000000, 19.0500000000]);
										}
										translate(v = [76.2000000000, -23.0500000000]) {
											square(center = true, size = [19.0500000000, 19.0500000000]);
										}
										translate(v = [57.1500000000, -18.0500000000]) {
											square(center = true, size = [19.0500000000, 19.0500000000]);
										}
										translate(v = [38.1000000000, -14.0500000000]) {
											square(center = true, size = [19.0500000000, 19.0500000000]);
										}
										translate(v = [19.0500000000, -19.0500000000]) {
											square(center = true, size = [19.0500000000, 19.0500000000]);
										}
										translate(v = [0.0000000000, -20.0500000000]) {
											square(center = true, size = [19.0500000000, 19.0500000000]);
										}
										translate(v = [95.2500000000, -5.0000000000]) {
											square(center = true, size = [19.0500000000, 19.0500000000]);
										}
										translate(v = [76.2000000000, -4.0000000000]) {
											square(center = true, size = [19.0500000000, 19.0500000000]);
										}
										translate(v = [57.1500000000, 1.0000000000]) {
											square(center = true, size = [19.0500000000, 19.0500000000]);
										}
										translate(v = [38.1000000000, 5.0000000000]) {
											square(center = true, size = [19.0500000000, 19.0500000000]);
										}
										translate(v = [19.0500000000, -0.0000000000]) {
											square(center = true, size = [19.0500000000, 19.0500000000]);
										}
										translate(v = [0.0000000000, -1.0000000000]) {
											square(center = true, size = [19.0500000000, 19.0500000000]);
										}
									}
								}
								offset(r = 4) {
									union() {
										translate(v = [0, 12]) {
											circle(r = 2.2500000000);
										}
										translate(v = [0, -94]) {
											circle(r = 2.2500000000);
										}
										translate(v = [81.7250000000, 12]) {
											circle(r = 2.2500000000);
										}
										translate(v = [81.7250000000, -94]) {
											circle(r = 2.2500000000);
										}
									}
								}
							}
						}
					}
					translate(v = [13.4000000000, -78.5000000000]) {
						rotate(a = -6.6000000000) {
							translate(v = [-7.8000000000, -7.0000000000]) {
								polygon(paths = [[0, 1, 2, 3, 4, 5, 6, 7, 8, 9, 10, 11, 12, 13, 14, 15, 16, 17, 18, 19]], points = [[0.8000000000, 0], [14.8000000000, 0], [14.8000000000, 1], [15.6000000000, 1], [15.6000000000, 4.5000000000], [14.8000000000, 4.5000000000], [14.8000000000, 9.5000000000], [15.6000000000, 9.5000000000], [15.6000000000, 13], [14.8000000000, 13], [14.8000000000, 14], [0.8000000000, 14], [0.8000000000, 13], [0, 13], [0, 9.5000000000], [0.8000000000, 9.5000000000], [0.8000000000, 4.5000000000], [0, 4.5000000000], [0, 1], [0.8000000000, 1]]);
							}
						}
					}
					translate(v = [-9.3000000000, -79.9000000000]) {
						rotate(a = 18.0000000000) {
							translate(v = [-7.8000000000, -7.0000000000]) {
								polygon(paths = [[0, 1, 2, 3, 4, 5, 6, 7, 8, 9, 10, 11, 12, 13, 14, 15, 16, 17, 18, 19]], points = [[0.8000000000, 0], [14.8000000000, 0], [14.8000000000, 1], [15.6000000000, 1], [15.6000000000, 4.5000000000], [14.8000000000, 4.5000000000], [14.8000000000, 9.5000000000], [15.6000000000, 9.5000000000], [15.6000000000, 13], [14.8000000000, 13], [14.8000000000, 14], [0.8000000000, 14], [0.8000000000, 13], [0, 13], [0, 9.5000000000], [0.8000000000, 9.5000000000], [0.8000000000, 4.5000000000], [0, 4.5000000000], [0, 1], [0.8000000000, 1]]);
							}
						}
					}
					translate(v = [-28.0000000000, -91.2000000000]) {
						rotate(a = 35.0000000000) {
							translate(v = [-7.8000000000, -7.0000000000]) {
								polygon(paths = [[0, 1, 2, 3, 4, 5, 6, 7, 8, 9, 10, 11, 12, 13, 14, 15, 16, 17, 18, 19]], points = [[0.8000000000, 0], [14.8000000000, 0], [14.8000000000, 1], [15.6000000000, 1], [15.6000000000, 4.5000000000], [14.8000000000, 4.5000000000], [14.8000000000, 9.5000000000], [15.6000000000, 9.5000000000], [15.6000000000, 13], [14.8000000000, 13], [14.8000000000, 14], [0.8000000000, 14], [0.8000000000, 13], [0, 13], [0, 9.5000000000], [0.8000000000, 9.5000000000], [0.8000000000, 4.5000000000], [0, 4.5000000000], [0, 1], [0.8000000000, 1]]);
							}
						}
					}
					translate(v = [95.2500000000, -62.1500000000]) {
						translate(v = [-7.8000000000, -7.0000000000]) {
							polygon(paths = [[0, 1, 2, 3, 4, 5, 6, 7, 8, 9, 10, 11, 12, 13, 14, 15, 16, 17, 18, 19]], points = [[0.8000000000, 0], [14.8000000000, 0], [14.8000000000, 1], [15.6000000000, 1], [15.6000000000, 4.5000000000], [14.8000000000, 4.5000000000], [14.8000000000, 9.5000000000], [15.6000000000, 9.5000000000], [15.6000000000, 13], [14.8000000000, 13], [14.8000000000, 14], [0.8000000000, 14], [0.8000000000, 13], [0, 13], [0, 9.5000000000], [0.8000000000, 9.5000000000], [0.8000000000, 4.5000000000], [0, 4.5000000000], [0, 1], [0.8000000000, 1]]);
						}
					}
					translate(v = [76.2000000000, -61.1500000000]) {
						translate(v = [-7.8000000000, -7.0000000000]) {
							polygon(paths = [[0, 1, 2, 3, 4, 5, 6, 7, 8, 9, 10, 11, 12, 13, 14, 15, 16, 17, 18, 19]], points = [[0.8000000000, 0], [14.8000000000, 0], [14.8000000000, 1], [15.6000000000, 1], [15.6000000000, 4.5000000000], [14.8000000000, 4.5000000000], [14.8000000000, 9.5000000000], [15.6000000000, 9.5000000000], [15.6000000000, 13], [14.8000000000, 13], [14.8000000000, 14], [0.8000000000, 14], [0.8000000000, 13], [0, 13], [0, 9.5000000000], [0.8000000000, 9.5000000000], [0.8000000000, 4.5000000000], [0, 4.5000000000], [0, 1], [0.8000000000, 1]]);
						}
					}
					translate(v = [57.1500000000, -56.1500000000]) {
						translate(v = [-7.8000000000, -7.0000000000]) {
							polygon(paths = [[0, 1, 2, 3, 4, 5, 6, 7, 8, 9, 10, 11, 12, 13, 14, 15, 16, 17, 18, 19]], points = [[0.8000000000, 0], [14.8000000000, 0], [14.8000000000, 1], [15.6000000000, 1], [15.6000000000, 4.5000000000], [14.8000000000, 4.5000000000], [14.8000000000, 9.5000000000], [15.6000000000, 9.5000000000], [15.6000000000, 13], [14.8000000000, 13], [14.8000000000, 14], [0.8000000000, 14], [0.8000000000, 13], [0, 13], [0, 9.5000000000], [0.8000000000, 9.5000000000], [0.8000000000, 4.5000000000], [0, 4.5000000000], [0, 1], [0.8000000000, 1]]);
						}
					}
					translate(v = [38.1000000000, -52.1500000000]) {
						translate(v = [-7.8000000000, -7.0000000000]) {
							polygon(paths = [[0, 1, 2, 3, 4, 5, 6, 7, 8, 9, 10, 11, 12, 13, 14, 15, 16, 17, 18, 19]], points = [[0.8000000000, 0], [14.8000000000, 0], [14.8000000000, 1], [15.6000000000, 1], [15.6000000000, 4.5000000000], [14.8000000000, 4.5000000000], [14.8000000000, 9.5000000000], [15.6000000000, 9.5000000000], [15.6000000000, 13], [14.8000000000, 13], [14.8000000000, 14], [0.8000000000, 14], [0.8000000000, 13], [0, 13], [0, 9.5000000000], [0.8000000000, 9.5000000000], [0.8000000000, 4.5000000000], [0, 4.5000000000], [0, 1], [0.8000000000, 1]]);
						}
					}
					translate(v = [19.0500000000, -57.1500000000]) {
						translate(v = [-7.8000000000, -7.0000000000]) {
							polygon(paths = [[0, 1, 2, 3, 4, 5, 6, 7, 8, 9, 10, 11, 12, 13, 14, 15, 16, 17, 18, 19]], points = [[0.8000000000, 0], [14.8000000000, 0], [14.8000000000, 1], [15.6000000000, 1], [15.6000000000, 4.5000000000], [14.8000000000, 4.5000000000], [14.8000000000, 9.5000000000], [15.6000000000, 9.5000000000], [15.6000000000, 13], [14.8000000000, 13], [14.8000000000, 14], [0.8000000000, 14], [0.8000000000, 13], [0, 13], [0, 9.5000000000], [0.8000000000, 9.5000000000], [0.8000000000, 4.5000000000], [0, 4.5000000000], [0, 1], [0.8000000000, 1]]);
						}
					}
					translate(v = [0.0000000000, -58.1500000000]) {
						translate(v = [-7.8000000000, -7.0000000000]) {
							polygon(paths = [[0, 1, 2, 3, 4, 5, 6, 7, 8, 9, 10, 11, 12, 13, 14, 15, 16, 17, 18, 19]], points = [[0.8000000000, 0], [14.8000000000, 0], [14.8000000000, 1], [15.6000000000, 1], [15.6000000000, 4.5000000000], [14.8000000000, 4.5000000000], [14.8000000000, 9.5000000000], [15.6000000000, 9.5000000000], [15.6000000000, 13], [14.8000000000, 13], [14.8000000000, 14], [0.8000000000, 14], [0.8000000000, 13], [0, 13], [0, 9.5000000000], [0.8000000000, 9.5000000000], [0.8000000000, 4.5000000000], [0, 4.5000000000], [0, 1], [0.8000000000, 1]]);
						}
					}
					translate(v = [95.2500000000, -43.1000000000]) {
						translate(v = [-7.8000000000, -7.0000000000]) {
							polygon(paths = [[0, 1, 2, 3, 4, 5, 6, 7, 8, 9, 10, 11, 12, 13, 14, 15, 16, 17, 18, 19]], points = [[0.8000000000, 0], [14.8000000000, 0], [14.8000000000, 1], [15.6000000000, 1], [15.6000000000, 4.5000000000], [14.8000000000, 4.5000000000], [14.8000000000, 9.5000000000], [15.6000000000, 9.5000000000], [15.6000000000, 13], [14.8000000000, 13], [14.8000000000, 14], [0.8000000000, 14], [0.8000000000, 13], [0, 13], [0, 9.5000000000], [0.8000000000, 9.5000000000], [0.8000000000, 4.5000000000], [0, 4.5000000000], [0, 1], [0.8000000000, 1]]);
						}
					}
					translate(v = [76.2000000000, -42.1000000000]) {
						translate(v = [-7.8000000000, -7.0000000000]) {
							polygon(paths = [[0, 1, 2, 3, 4, 5, 6, 7, 8, 9, 10, 11, 12, 13, 14, 15, 16, 17, 18, 19]], points = [[0.8000000000, 0], [14.8000000000, 0], [14.8000000000, 1], [15.6000000000, 1], [15.6000000000, 4.5000000000], [14.8000000000, 4.5000000000], [14.8000000000, 9.5000000000], [15.6000000000, 9.5000000000], [15.6000000000, 13], [14.8000000000, 13], [14.8000000000, 14], [0.8000000000, 14], [0.8000000000, 13], [0, 13], [0, 9.5000000000], [0.8000000000, 9.5000000000], [0.8000000000, 4.5000000000], [0, 4.5000000000], [0, 1], [0.8000000000, 1]]);
						}
					}
					translate(v = [57.1500000000, -37.1000000000]) {
						translate(v = [-7.8000000000, -7.0000000000]) {
							polygon(paths = [[0, 1, 2, 3, 4, 5, 6, 7, 8, 9, 10, 11, 12, 13, 14, 15, 16, 17, 18, 19]], points = [[0.8000000000, 0], [14.8000000000, 0], [14.8000000000, 1], [15.6000000000, 1], [15.6000000000, 4.5000000000], [14.8000000000, 4.5000000000], [14.8000000000, 9.5000000000], [15.6000000000, 9.5000000000], [15.6000000000, 13], [14.8000000000, 13], [14.8000000000, 14], [0.8000000000, 14], [0.8000000000, 13], [0, 13], [0, 9.5000000000], [0.8000000000, 9.5000000000], [0.8000000000, 4.5000000000], [0, 4.5000000000], [0, 1], [0.8000000000, 1]]);
						}
					}
					translate(v = [38.1000000000, -33.1000000000]) {
						translate(v = [-7.8000000000, -7.0000000000]) {
							polygon(paths = [[0, 1, 2, 3, 4, 5, 6, 7, 8, 9, 10, 11, 12, 13, 14, 15, 16, 17, 18, 19]], points = [[0.8000000000, 0], [14.8000000000, 0], [14.8000000000, 1], [15.6000000000, 1], [15.6000000000, 4.5000000000], [14.8000000000, 4.5000000000], [14.8000000000, 9.5000000000], [15.6000000000, 9.5000000000], [15.6000000000, 13], [14.8000000000, 13], [14.8000000000, 14], [0.8000000000, 14], [0.8000000000, 13], [0, 13], [0, 9.5000000000], [0.8000000000, 9.5000000000], [0.8000000000, 4.5000000000], [0, 4.5000000000], [0, 1], [0.8000000000, 1]]);
						}
					}
					translate(v = [19.0500000000, -38.1000000000]) {
						translate(v = [-7.8000000000, -7.0000000000]) {
							polygon(paths = [[0, 1, 2, 3, 4, 5, 6, 7, 8, 9, 10, 11, 12, 13, 14, 15, 16, 17, 18, 19]], points = [[0.8000000000, 0], [14.8000000000, 0], [14.8000000000, 1], [15.6000000000, 1], [15.6000000000, 4.5000000000], [14.8000000000, 4.5000000000], [14.8000000000, 9.5000000000], [15.6000000000, 9.5000000000], [15.6000000000, 13], [14.8000000000, 13], [14.8000000000, 14], [0.8000000000, 14], [0.8000000000, 13], [0, 13], [0, 9.5000000000], [0.8000000000, 9.5000000000], [0.8000000000, 4.5000000000], [0, 4.5000000000], [0, 1], [0.8000000000, 1]]);
						}
					}
					translate(v = [0.0000000000, -39.1000000000]) {
						translate(v = [-7.8000000000, -7.0000000000]) {
							polygon(paths = [[0, 1, 2, 3, 4, 5, 6, 7, 8, 9, 10, 11, 12, 13, 14, 15, 16, 17, 18, 19]], points = [[0.8000000000, 0], [14.8000000000, 0], [14.8000000000, 1], [15.6000000000, 1], [15.6000000000, 4.5000000000], [14.8000000000, 4.5000000000], [14.8000000000, 9.5000000000], [15.6000000000, 9.5000000000], [15.6000000000, 13], [14.8000000000, 13], [14.8000000000, 14], [0.8000000000, 14], [0.8000000000, 13], [0, 13], [0, 9.5000000000], [0.8000000000, 9.5000000000], [0.8000000000, 4.5000000000], [0, 4.5000000000], [0, 1], [0.8000000000, 1]]);
						}
					}
					translate(v = [95.2500000000, -24.0500000000]) {
						translate(v = [-7.8000000000, -7.0000000000]) {
							polygon(paths = [[0, 1, 2, 3, 4, 5, 6, 7, 8, 9, 10, 11, 12, 13, 14, 15, 16, 17, 18, 19]], points = [[0.8000000000, 0], [14.8000000000, 0], [14.8000000000, 1], [15.6000000000, 1], [15.6000000000, 4.5000000000], [14.8000000000, 4.5000000000], [14.8000000000, 9.5000000000], [15.6000000000, 9.5000000000], [15.6000000000, 13], [14.8000000000, 13], [14.8000000000, 14], [0.8000000000, 14], [0.8000000000, 13], [0, 13], [0, 9.5000000000], [0.8000000000, 9.5000000000], [0.8000000000, 4.5000000000], [0, 4.5000000000], [0, 1], [0.8000000000, 1]]);
						}
					}
					translate(v = [76.2000000000, -23.0500000000]) {
						translate(v = [-7.8000000000, -7.0000000000]) {
							polygon(paths = [[0, 1, 2, 3, 4, 5, 6, 7, 8, 9, 10, 11, 12, 13, 14, 15, 16, 17, 18, 19]], points = [[0.8000000000, 0], [14.8000000000, 0], [14.8000000000, 1], [15.6000000000, 1], [15.6000000000, 4.5000000000], [14.8000000000, 4.5000000000], [14.8000000000, 9.5000000000], [15.6000000000, 9.5000000000], [15.6000000000, 13], [14.8000000000, 13], [14.8000000000, 14], [0.8000000000, 14], [0.8000000000, 13], [0, 13], [0, 9.5000000000], [0.8000000000, 9.5000000000], [0.8000000000, 4.5000000000], [0, 4.5000000000], [0, 1], [0.8000000000, 1]]);
						}
					}
					translate(v = [57.1500000000, -18.0500000000]) {
						translate(v = [-7.8000000000, -7.0000000000]) {
							polygon(paths = [[0, 1, 2, 3, 4, 5, 6, 7, 8, 9, 10, 11, 12, 13, 14, 15, 16, 17, 18, 19]], points = [[0.8000000000, 0], [14.8000000000, 0], [14.8000000000, 1], [15.6000000000, 1], [15.6000000000, 4.5000000000], [14.8000000000, 4.5000000000], [14.8000000000, 9.5000000000], [15.6000000000, 9.5000000000], [15.6000000000, 13], [14.8000000000, 13], [14.8000000000, 14], [0.8000000000, 14], [0.8000000000, 13], [0, 13], [0, 9.5000000000], [0.8000000000, 9.5000000000], [0.8000000000, 4.5000000000], [0, 4.5000000000], [0, 1], [0.8000000000, 1]]);
						}
					}
					translate(v = [38.1000000000, -14.0500000000]) {
						translate(v = [-7.8000000000, -7.0000000000]) {
							polygon(paths = [[0, 1, 2, 3, 4, 5, 6, 7, 8, 9, 10, 11, 12, 13, 14, 15, 16, 17, 18, 19]], points = [[0.8000000000, 0], [14.8000000000, 0], [14.8000000000, 1], [15.6000000000, 1], [15.6000000000, 4.5000000000], [14.8000000000, 4.5000000000], [14.8000000000, 9.5000000000], [15.6000000000, 9.5000000000], [15.6000000000, 13], [14.8000000000, 13], [14.8000000000, 14], [0.8000000000, 14], [0.8000000000, 13], [0, 13], [0, 9.5000000000], [0.8000000000, 9.5000000000], [0.8000000000, 4.5000000000], [0, 4.5000000000], [0, 1], [0.8000000000, 1]]);
						}
					}
					translate(v = [19.0500000000, -19.0500000000]) {
						translate(v = [-7.8000000000, -7.0000000000]) {
							polygon(paths = [[0, 1, 2, 3, 4, 5, 6, 7, 8, 9, 10, 11, 12, 13, 14, 15, 16, 17, 18, 19]], points = [[0.8000000000, 0], [14.8000000000, 0], [14.8000000000, 1], [15.6000000000, 1], [15.6000000000, 4.5000000000], [14.8000000000, 4.5000000000], [14.8000000000, 9.5000000000], [15.6000000000, 9.5000000000], [15.6000000000, 13], [14.8000000000, 13], [14.8000000000, 14], [0.8000000000, 14], [0.8000000000, 13], [0, 13], [0, 9.5000000000], [0.8000000000, 9.5000000000], [0.8000000000, 4.5000000000], [0, 4.5000000000], [0, 1], [0.8000000000, 1]]);
						}
					}
					translate(v = [0.0000000000, -20.0500000000]) {
						translate(v = [-7.8000000000, -7.0000000000]) {
							polygon(paths = [[0, 1, 2, 3, 4, 5, 6, 7, 8, 9, 10, 11, 12, 13, 14, 15, 16, 17, 18, 19]], points = [[0.8000000000, 0], [14.8000000000, 0], [14.8000000000, 1], [15.6000000000, 1], [15.6000000000, 4.5000000000], [14.8000000000, 4.5000000000], [14.8000000000, 9.5000000000], [15.6000000000, 9.5000000000], [15.6000000000, 13], [14.8000000000, 13], [14.8000000000, 14], [0.8000000000, 14], [0.8000000000, 13], [0, 13], [0, 9.5000000000], [0.8000000000, 9.5000000000], [0.8000000000, 4.5000000000], [0, 4.5000000000], [0, 1], [0.8000000000, 1]]);
						}
					}
					translate(v = [95.2500000000, -5.0000000000]) {
						translate(v = [-7.8000000000, -7.0000000000]) {
							polygon(paths = [[0, 1, 2, 3, 4, 5, 6, 7, 8, 9, 10, 11, 12, 13, 14, 15, 16, 17, 18, 19]], points = [[0.8000000000, 0], [14.8000000000, 0], [14.8000000000, 1], [15.6000000000, 1], [15.6000000000, 4.5000000000], [14.8000000000, 4.5000000000], [14.8000000000, 9.5000000000], [15.6000000000, 9.5000000000], [15.6000000000, 13], [14.8000000000, 13], [14.8000000000, 14], [0.8000000000, 14], [0.8000000000, 13], [0, 13], [0, 9.5000000000], [0.8000000000, 9.5000000000], [0.8000000000, 4.5000000000], [0, 4.5000000000], [0, 1], [0.8000000000, 1]]);
						}
					}
					translate(v = [76.2000000000, -4.0000000000]) {
						translate(v = [-7.8000000000, -7.0000000000]) {
							polygon(paths = [[0, 1, 2, 3, 4, 5, 6, 7, 8, 9, 10, 11, 12, 13, 14, 15, 16, 17, 18, 19]], points = [[0.8000000000, 0], [14.8000000000, 0], [14.8000000000, 1], [15.6000000000, 1], [15.6000000000, 4.5000000000], [14.8000000000, 4.5000000000], [14.8000000000, 9.5000000000], [15.6000000000, 9.5000000000], [15.6000000000, 13], [14.8000000000, 13], [14.8000000000, 14], [0.8000000000, 14], [0.8000000000, 13], [0, 13], [0, 9.5000000000], [0.8000000000, 9.5000000000], [0.8000000000, 4.5000000000], [0, 4.5000000000], [0, 1], [0.8000000000, 1]]);
						}
					}
					translate(v = [57.1500000000, 1.0000000000]) {
						translate(v = [-7.8000000000, -7.0000000000]) {
							polygon(paths = [[0, 1, 2, 3, 4, 5, 6, 7, 8, 9, 10, 11, 12, 13, 14, 15, 16, 17, 18, 19]], points = [[0.8000000000, 0], [14.8000000000, 0], [14.8000000000, 1], [15.6000000000, 1], [15.6000000000, 4.5000000000], [14.8000000000, 4.5000000000], [14.8000000000, 9.5000000000], [15.6000000000, 9.5000000000], [15.6000000000, 13], [14.8000000000, 13], [14.8000000000, 14], [0.8000000000, 14], [0.8000000000, 13], [0, 13], [0, 9.5000000000], [0.8000000000, 9.5000000000], [0.8000000000, 4.5000000000], [0, 4.5000000000], [0, 1], [0.8000000000, 1]]);
						}
					}
					translate(v = [38.1000000000, 5.0000000000]) {
						translate(v = [-7.8000000000, -7.0000000000]) {
							polygon(paths = [[0, 1, 2, 3, 4, 5, 6, 7, 8, 9, 10, 11, 12, 13, 14, 15, 16, 17, 18, 19]], points = [[0.8000000000, 0], [14.8000000000, 0], [14.8000000000, 1], [15.6000000000, 1], [15.6000000000, 4.5000000000], [14.8000000000, 4.5000000000], [14.8000000000, 9.5000000000], [15.6000000000, 9.5000000000], [15.6000000000, 13], [14.8000000000, 13], [14.8000000000, 14], [0.8000000000, 14], [0.8000000000, 13], [0, 13], [0, 9.5000000000], [0.8000000000, 9.5000000000], [0.8000000000, 4.5000000000], [0, 4.5000000000], [0, 1], [0.8000000000, 1]]);
						}
					}
					translate(v = [19.0500000000, -0.0000000000]) {
						translate(v = [-7.8000000000, -7.0000000000]) {
							polygon(paths = [[0, 1, 2, 3, 4, 5, 6, 7, 8, 9, 10, 11, 12, 13, 14, 15, 16, 17, 18, 19]], points = [[0.8000000000, 0], [14.8000000000, 0], [14.8000000000, 1], [15.6000000000, 1], [15.6000000000, 4.5000000000], [14.8000000000, 4.5000000000], [14.8000000000, 9.5000000000], [15.6000000000, 9.5000000000], [15.6000000000, 13], [14.8000000000, 13], [14.8000000000, 14], [0.8000000000, 14], [0.8000000000, 13], [0, 13], [0, 9.5000000000], [0.8000000000, 9.5000000000], [0.8000000000, 4.5000000000], [0, 4.5000000000], [0, 1], [0.8000000000, 1]]);
						}
					}
					translate(v = [0.0000000000, -1.0000000000]) {
						translate(v = [-7.8000000000, -7.0000000000]) {
							polygon(paths = [[0, 1, 2, 3, 4, 5, 6, 7, 8, 9, 10, 11, 12, 13, 14, 15, 16, 17, 18, 19]], points = [[0.8000000000, 0], [14.8000000000, 0], [14.8000000000, 1], [15.6000000000, 1], [15.6000000000, 4.5000000000], [14.8000000000, 4.5000000000], [14.8000000000, 9.5000000000], [15.6000000000, 9.5000000000], [15.6000000000, 13], [14.8000000000, 13], [14.8000000000, 14], [0.8000000000, 14], [0.8000000000, 13], [0, 13], [0, 9.5000000000], [0.8000000000, 9.5000000000], [0.8000000000, 4.5000000000], [0, 4.5000000000], [0, 1], [0.8000000000, 1]]);
						}
					}
				}
			}
		}
	}
	translate(v = [0, 0, 10]) {
		color(c = [0.8000000000, 0.8500000000, 1, 0.5000000000]) {
			linear_extrude(height = 1.6000000000) {
				offset(r = 2) {
					offset(r = -2) {
						difference() {
							offset(r = -2) {
								offset(r = 2) {
									union() {
										offset(r = -12) {
											offset(r = 16) {
												intersection() {
													offset(r = -10) {
														offset(r = 10) {
															translate(v = [-16.2000000000, -42.8000000000]) {
																rotate(a = 180.0000000000) {
																	polygon(paths = [[0, 1, 2, 3]], points = [[-1.5000000000, 1.5000000000], [8, 1.5000000000], [8, -6], [-1.5000000000, -6]]);
																}
															}
															translate(v = [-40.0000000000, -2.0000000000]) {
																color(c = [0.3000000000, 0.3000000000, 0.3000000000]) {
																	mirror(v = [0, 1, 0]) {
																		polygon(paths = [[0, 1, 2, 3, 4, 5, 6, 7]], points = [[-5.3500000000, 12.1000000000], [5.3500000000, 12.1000000000], [5.3500000000, 0], [5.1000000000, 0], [5.1000000000, -2], [-5.1000000000, -2], [-5.1000000000, 0], [-5.3500000000, 0]]);
																	}
																}
															}
															translate(v = [-24.0000000000, -17.8000000000]) {
																rotate(a = -90.0000000000) {
																	color(c = [0.0040000000, 0.2274509804, 0.5764705882, 0.5000000000]) {
																		polygon(paths = [[0, 1, 2, 3]], points = [[-17.8000000000, 8.9000000000], [15.2000000000, 8.9000000000], [15.2000000000, -8.9000000000], [-17.8000000000, -8.9000000000]]);
																	}
																}
															}
															translate(v = [-39.8000000000, -21.2000000000]) {
																rotate(a = -90.0000000000) {
																	polygon(paths = [[0, 1, 2, 3]], points = [[-4.7000000000, -1.1000000000], [4.7000000000, -1.1000000000], [4.7000000000, 1.1000000000], [-4.7000000000, 1.1000000000]]);
																}
															}
															translate(v = [-43.3000000000, -21.2000000000]) {
																rotate(a = -90.0000000000) {
																	polygon(paths = [[0, 1, 2, 3]], points = [[-4.7000000000, -1.1000000000], [4.7000000000, -1.1000000000], [4.7000000000, 1.1000000000], [-4.7000000000, 1.1000000000]]);
																}
															}
															translate(v = [-36.1000000000, -18.6000000000]) {
																rotate(a = 180.0000000000) {
																	polygon(paths = [[0, 1, 2, 3]], points = [[-1.6500000000, -1.2400000000], [1.6500000000, -1.2400000000], [1.6500000000, 1.2400000000], [-1.6500000000, 1.2400000000]]);
																}
															}
															translate(v = [-36.1000000000, -24.4000000000]) {
																polygon(paths = [[0, 1, 2, 3]], points = [[-1.6500000000, -1.2400000000], [1.6500000000, -1.2400000000], [1.6500000000, 1.2400000000], [-1.6500000000, 1.2400000000]]);
															}
														}
													}
													translate(v = [0, -4]) {
														offset(r = -10) {
															offset(r = 10) {
																translate(v = [-16.2000000000, -42.8000000000]) {
																	rotate(a = 180.0000000000) {
																		polygon(paths = [[0, 1, 2, 3]], points = [[-1.5000000000, 1.5000000000], [8, 1.5000000000], [8, -6], [-1.5000000000, -6]]);
																	}
																}
																translate(v = [-40.0000000000, -2.0000000000]) {
																	color(c = [0.3000000000, 0.3000000000, 0.3000000000]) {
																		mirror(v = [0, 1, 0]) {
																			polygon(paths = [[0, 1, 2, 3, 4, 5, 6, 7]], points = [[-5.3500000000, 12.1000000000], [5.3500000000, 12.1000000000], [5.3500000000, 0], [5.1000000000, 0], [5.1000000000, -2], [-5.1000000000, -2], [-5.1000000000, 0], [-5.3500000000, 0]]);
																		}
																	}
																}
																translate(v = [-24.0000000000, -17.8000000000]) {
																	rotate(a = -90.0000000000) {
																		color(c = [0.0040000000, 0.2274509804, 0.5764705882, 0.5000000000]) {
																			polygon(paths = [[0, 1, 2, 3]], points = [[-17.8000000000, 8.9000000000], [15.2000000000, 8.9000000000], [15.2000000000, -8.9000000000], [-17.8000000000, -8.9000000000]]);
																		}
																	}
																}
																translate(v = [-39.8000000000, -21.2000000000]) {
																	rotate(a = -90.0000000000) {
																		polygon(paths = [[0, 1, 2, 3]], points = [[-4.7000000000, -1.1000000000], [4.7000000000, -1.1000000000], [4.7000000000, 1.1000000000], [-4.7000000000, 1.1000000000]]);
																	}
																}
																translate(v = [-43.3000000000, -21.2000000000]) {
																	rotate(a = -90.0000000000) {
																		polygon(paths = [[0, 1, 2, 3]], points = [[-4.7000000000, -1.1000000000], [4.7000000000, -1.1000000000], [4.7000000000, 1.1000000000], [-4.7000000000, 1.1000000000]]);
																	}
																}
																translate(v = [-36.1000000000, -18.6000000000]) {
																	rotate(a = 180.0000000000) {
																		polygon(paths = [[0, 1, 2, 3]], points = [[-1.6500000000, -1.2400000000], [1.6500000000, -1.2400000000], [1.6500000000, 1.2400000000], [-1.6500000000, 1.2400000000]]);
																	}
																}
																translate(v = [-36.1000000000, -24.4000000000]) {
																	polygon(paths = [[0, 1, 2, 3]], points = [[-1.6500000000, -1.2400000000], [1.6500000000, -1.2400000000], [1.6500000000, 1.2400000000], [-1.6500000000, 1.2400000000]]);
																}
															}
														}
													}
												}
											}
										}
										offset(r = 2) {
											union() {
												translate(v = [63.6750000000, -68.6750000000]) {
													circle(r = 1.2500000000);
												}
												translate(v = [69.6750000000, 8.5250000000]) {
													circle(r = 1.2500000000);
												}
												translate(v = [25.5750000000, 12.5250000000]) {
													circle(r = 1.2500000000);
												}
												translate(v = [-31.0000000000, -39.0000000000]) {
													circle(r = 1.2500000000);
												}
												translate(v = [-18.0000000000, -48.0000000000]) {
													circle(r = 1.2500000000);
												}
												translate(v = [-44.0000000000, -30.0000000000]) {
													circle(r = 1.2500000000);
												}
											}
										}
									}
								}
							}
							translate(v = [-2, 0, 0]) {
								difference() {
									offset(r = -20) {
										offset(r = 20) {
											union() {
												offset(r = -13) {
													offset(r = 16) {
														translate(v = [13.4000000000, -78.5000000000]) {
															rotate(a = -6.6000000000) {
																square(center = true, size = [19.0500000000, 19.0500000000]);
															}
														}
														translate(v = [-9.3000000000, -79.9000000000]) {
															rotate(a = 18.0000000000) {
																square(center = true, size = [19.0500000000, 19.0500000000]);
															}
														}
														translate(v = [-28.0000000000, -91.2000000000]) {
															rotate(a = 35.0000000000) {
																square(center = true, size = [19.0500000000, 19.0500000000]);
															}
														}
														translate(v = [95.2500000000, -62.1500000000]) {
															square(center = true, size = [19.0500000000, 19.0500000000]);
														}
														translate(v = [76.2000000000, -61.1500000000]) {
															square(center = true, size = [19.0500000000, 19.0500000000]);
														}
														translate(v = [57.1500000000, -56.1500000000]) {
															square(center = true, size = [19.0500000000, 19.0500000000]);
														}
														translate(v = [38.1000000000, -52.1500000000]) {
															square(center = true, size = [19.0500000000, 19.0500000000]);
														}
														translate(v = [19.0500000000, -57.1500000000]) {
															square(center = true, size = [19.0500000000, 19.0500000000]);
														}
														translate(v = [0.0000000000, -58.1500000000]) {
															square(center = true, size = [19.0500000000, 19.0500000000]);
														}
														translate(v = [95.2500000000, -43.1000000000]) {
															square(center = true, size = [19.0500000000, 19.0500000000]);
														}
														translate(v = [76.2000000000, -42.1000000000]) {
															square(center = true, size = [19.0500000000, 19.0500000000]);
														}
														translate(v = [57.1500000000, -37.1000000000]) {
															square(center = true, size = [19.0500000000, 19.0500000000]);
														}
														translate(v = [38.1000000000, -33.1000000000]) {
															square(center = true, size = [19.0500000000, 19.0500000000]);
														}
														translate(v = [19.0500000000, -38.1000000000]) {
															square(center = true, size = [19.0500000000, 19.0500000000]);
														}
														translate(v = [0.0000000000, -39.1000000000]) {
															square(center = true, size = [19.0500000000, 19.0500000000]);
														}
														translate(v = [95.2500000000, -24.0500000000]) {
															square(center = true, size = [19.0500000000, 19.0500000000]);
														}
														translate(v = [76.2000000000, -23.0500000000]) {
															square(center = true, size = [19.0500000000, 19.0500000000]);
														}
														translate(v = [57.1500000000, -18.0500000000]) {
															square(center = true, size = [19.0500000000, 19.0500000000]);
														}
														translate(v = [38.1000000000, -14.0500000000]) {
															square(center = true, size = [19.0500000000, 19.0500000000]);
														}
														translate(v = [19.0500000000, -19.0500000000]) {
															square(center = true, size = [19.0500000000, 19.0500000000]);
														}
														translate(v = [0.0000000000, -20.0500000000]) {
															square(center = true, size = [19.0500000000, 19.0500000000]);
														}
														translate(v = [95.2500000000, -5.0000000000]) {
															square(center = true, size = [19.0500000000, 19.0500000000]);
														}
														translate(v = [76.2000000000, -4.0000000000]) {
															square(center = true, size = [19.0500000000, 19.0500000000]);
														}
														translate(v = [57.1500000000, 1.0000000000]) {
															square(center = true, size = [19.0500000000, 19.0500000000]);
														}
														translate(v = [38.1000000000, 5.0000000000]) {
															square(center = true, size = [19.0500000000, 19.0500000000]);
														}
														translate(v = [19.0500000000, -0.0000000000]) {
															square(center = true, size = [19.0500000000, 19.0500000000]);
														}
														translate(v = [0.0000000000, -1.0000000000]) {
															square(center = true, size = [19.0500000000, 19.0500000000]);
														}
													}
												}
												offset(r = 4) {
													union() {
														translate(v = [0, 12]) {
															circle(r = 2.2500000000);
														}
														translate(v = [0, -94]) {
															circle(r = 2.2500000000);
														}
														translate(v = [81.7250000000, 12]) {
															circle(r = 2.2500000000);
														}
														translate(v = [81.7250000000, -94]) {
															circle(r = 2.2500000000);
														}
													}
												}
											}
										}
									}
									translate(v = [13.4000000000, -78.5000000000]) {
										rotate(a = -6.6000000000) {
											translate(v = [-7.8000000000, -7.0000000000]) {
												polygon(paths = [[0, 1, 2, 3, 4, 5, 6, 7, 8, 9, 10, 11, 12, 13, 14, 15, 16, 17, 18, 19]], points = [[0.8000000000, 0], [14.8000000000, 0], [14.8000000000, 1], [15.6000000000, 1], [15.6000000000, 4.5000000000], [14.8000000000, 4.5000000000], [14.8000000000, 9.5000000000], [15.6000000000, 9.5000000000], [15.6000000000, 13], [14.8000000000, 13], [14.8000000000, 14], [0.8000000000, 14], [0.8000000000, 13], [0, 13], [0, 9.5000000000], [0.8000000000, 9.5000000000], [0.8000000000, 4.5000000000], [0, 4.5000000000], [0, 1], [0.8000000000, 1]]);
											}
										}
									}
									translate(v = [-9.3000000000, -79.9000000000]) {
										rotate(a = 18.0000000000) {
											translate(v = [-7.8000000000, -7.0000000000]) {
												polygon(paths = [[0, 1, 2, 3, 4, 5, 6, 7, 8, 9, 10, 11, 12, 13, 14, 15, 16, 17, 18, 19]], points = [[0.8000000000, 0], [14.8000000000, 0], [14.8000000000, 1], [15.6000000000, 1], [15.6000000000, 4.5000000000], [14.8000000000, 4.5000000000], [14.8000000000, 9.5000000000], [15.6000000000, 9.5000000000], [15.6000000000, 13], [14.8000000000, 13], [14.8000000000, 14], [0.8000000000, 14], [0.8000000000, 13], [0, 13], [0, 9.5000000000], [0.8000000000, 9.5000000000], [0.8000000000, 4.5000000000], [0, 4.5000000000], [0, 1], [0.8000000000, 1]]);
											}
										}
									}
									translate(v = [-28.0000000000, -91.2000000000]) {
										rotate(a = 35.0000000000) {
											translate(v = [-7.8000000000, -7.0000000000]) {
												polygon(paths = [[0, 1, 2, 3, 4, 5, 6, 7, 8, 9, 10, 11, 12, 13, 14, 15, 16, 17, 18, 19]], points = [[0.8000000000, 0], [14.8000000000, 0], [14.8000000000, 1], [15.6000000000, 1], [15.6000000000, 4.5000000000], [14.8000000000, 4.5000000000], [14.8000000000, 9.5000000000], [15.6000000000, 9.5000000000], [15.6000000000, 13], [14.8000000000, 13], [14.8000000000, 14], [0.8000000000, 14], [0.8000000000, 13], [0, 13], [0, 9.5000000000], [0.8000000000, 9.5000000000], [0.8000000000, 4.5000000000], [0, 4.5000000000], [0, 1], [0.8000000000, 1]]);
											}
										}
									}
									translate(v = [95.2500000000, -62.1500000000]) {
										translate(v = [-7.8000000000, -7.0000000000]) {
											polygon(paths = [[0, 1, 2, 3, 4, 5, 6, 7, 8, 9, 10, 11, 12, 13, 14, 15, 16, 17, 18, 19]], points = [[0.8000000000, 0], [14.8000000000, 0], [14.8000000000, 1], [15.6000000000, 1], [15.6000000000, 4.5000000000], [14.8000000000, 4.5000000000], [14.8000000000, 9.5000000000], [15.6000000000, 9.5000000000], [15.6000000000, 13], [14.8000000000, 13], [14.8000000000, 14], [0.8000000000, 14], [0.8000000000, 13], [0, 13], [0, 9.5000000000], [0.8000000000, 9.5000000000], [0.8000000000, 4.5000000000], [0, 4.5000000000], [0, 1], [0.8000000000, 1]]);
										}
									}
									translate(v = [76.2000000000, -61.1500000000]) {
										translate(v = [-7.8000000000, -7.0000000000]) {
											polygon(paths = [[0, 1, 2, 3, 4, 5, 6, 7, 8, 9, 10, 11, 12, 13, 14, 15, 16, 17, 18, 19]], points = [[0.8000000000, 0], [14.8000000000, 0], [14.8000000000, 1], [15.6000000000, 1], [15.6000000000, 4.5000000000], [14.8000000000, 4.5000000000], [14.8000000000, 9.5000000000], [15.6000000000, 9.5000000000], [15.6000000000, 13], [14.8000000000, 13], [14.8000000000, 14], [0.8000000000, 14], [0.8000000000, 13], [0, 13], [0, 9.5000000000], [0.8000000000, 9.5000000000], [0.8000000000, 4.5000000000], [0, 4.5000000000], [0, 1], [0.8000000000, 1]]);
										}
									}
									translate(v = [57.1500000000, -56.1500000000]) {
										translate(v = [-7.8000000000, -7.0000000000]) {
											polygon(paths = [[0, 1, 2, 3, 4, 5, 6, 7, 8, 9, 10, 11, 12, 13, 14, 15, 16, 17, 18, 19]], points = [[0.8000000000, 0], [14.8000000000, 0], [14.8000000000, 1], [15.6000000000, 1], [15.6000000000, 4.5000000000], [14.8000000000, 4.5000000000], [14.8000000000, 9.5000000000], [15.6000000000, 9.5000000000], [15.6000000000, 13], [14.8000000000, 13], [14.8000000000, 14], [0.8000000000, 14], [0.8000000000, 13], [0, 13], [0, 9.5000000000], [0.8000000000, 9.5000000000], [0.8000000000, 4.5000000000], [0, 4.5000000000], [0, 1], [0.8000000000, 1]]);
										}
									}
									translate(v = [38.1000000000, -52.1500000000]) {
										translate(v = [-7.8000000000, -7.0000000000]) {
											polygon(paths = [[0, 1, 2, 3, 4, 5, 6, 7, 8, 9, 10, 11, 12, 13, 14, 15, 16, 17, 18, 19]], points = [[0.8000000000, 0], [14.8000000000, 0], [14.8000000000, 1], [15.6000000000, 1], [15.6000000000, 4.5000000000], [14.8000000000, 4.5000000000], [14.8000000000, 9.5000000000], [15.6000000000, 9.5000000000], [15.6000000000, 13], [14.8000000000, 13], [14.8000000000, 14], [0.8000000000, 14], [0.8000000000, 13], [0, 13], [0, 9.5000000000], [0.8000000000, 9.5000000000], [0.8000000000, 4.5000000000], [0, 4.5000000000], [0, 1], [0.8000000000, 1]]);
										}
									}
									translate(v = [19.0500000000, -57.1500000000]) {
										translate(v = [-7.8000000000, -7.0000000000]) {
											polygon(paths = [[0, 1, 2, 3, 4, 5, 6, 7, 8, 9, 10, 11, 12, 13, 14, 15, 16, 17, 18, 19]], points = [[0.8000000000, 0], [14.8000000000, 0], [14.8000000000, 1], [15.6000000000, 1], [15.6000000000, 4.5000000000], [14.8000000000, 4.5000000000], [14.8000000000, 9.5000000000], [15.6000000000, 9.5000000000], [15.6000000000, 13], [14.8000000000, 13], [14.8000000000, 14], [0.8000000000, 14], [0.8000000000, 13], [0, 13], [0, 9.5000000000], [0.8000000000, 9.5000000000], [0.8000000000, 4.5000000000], [0, 4.5000000000], [0, 1], [0.8000000000, 1]]);
										}
									}
									translate(v = [0.0000000000, -58.1500000000]) {
										translate(v = [-7.8000000000, -7.0000000000]) {
											polygon(paths = [[0, 1, 2, 3, 4, 5, 6, 7, 8, 9, 10, 11, 12, 13, 14, 15, 16, 17, 18, 19]], points = [[0.8000000000, 0], [14.8000000000, 0], [14.8000000000, 1], [15.6000000000, 1], [15.6000000000, 4.5000000000], [14.8000000000, 4.5000000000], [14.8000000000, 9.5000000000], [15.6000000000, 9.5000000000], [15.6000000000, 13], [14.8000000000, 13], [14.8000000000, 14], [0.8000000000, 14], [0.8000000000, 13], [0, 13], [0, 9.5000000000], [0.8000000000, 9.5000000000], [0.8000000000, 4.5000000000], [0, 4.5000000000], [0, 1], [0.8000000000, 1]]);
										}
									}
									translate(v = [95.2500000000, -43.1000000000]) {
										translate(v = [-7.8000000000, -7.0000000000]) {
											polygon(paths = [[0, 1, 2, 3, 4, 5, 6, 7, 8, 9, 10, 11, 12, 13, 14, 15, 16, 17, 18, 19]], points = [[0.8000000000, 0], [14.8000000000, 0], [14.8000000000, 1], [15.6000000000, 1], [15.6000000000, 4.5000000000], [14.8000000000, 4.5000000000], [14.8000000000, 9.5000000000], [15.6000000000, 9.5000000000], [15.6000000000, 13], [14.8000000000, 13], [14.8000000000, 14], [0.8000000000, 14], [0.8000000000, 13], [0, 13], [0, 9.5000000000], [0.8000000000, 9.5000000000], [0.8000000000, 4.5000000000], [0, 4.5000000000], [0, 1], [0.8000000000, 1]]);
										}
									}
									translate(v = [76.2000000000, -42.1000000000]) {
										translate(v = [-7.8000000000, -7.0000000000]) {
											polygon(paths = [[0, 1, 2, 3, 4, 5, 6, 7, 8, 9, 10, 11, 12, 13, 14, 15, 16, 17, 18, 19]], points = [[0.8000000000, 0], [14.8000000000, 0], [14.8000000000, 1], [15.6000000000, 1], [15.6000000000, 4.5000000000], [14.8000000000, 4.5000000000], [14.8000000000, 9.5000000000], [15.6000000000, 9.5000000000], [15.6000000000, 13], [14.8000000000, 13], [14.8000000000, 14], [0.8000000000, 14], [0.8000000000, 13], [0, 13], [0, 9.5000000000], [0.8000000000, 9.5000000000], [0.8000000000, 4.5000000000], [0, 4.5000000000], [0, 1], [0.8000000000, 1]]);
										}
									}
									translate(v = [57.1500000000, -37.1000000000]) {
										translate(v = [-7.8000000000, -7.0000000000]) {
											polygon(paths = [[0, 1, 2, 3, 4, 5, 6, 7, 8, 9, 10, 11, 12, 13, 14, 15, 16, 17, 18, 19]], points = [[0.8000000000, 0], [14.8000000000, 0], [14.8000000000, 1], [15.6000000000, 1], [15.6000000000, 4.5000000000], [14.8000000000, 4.5000000000], [14.8000000000, 9.5000000000], [15.6000000000, 9.5000000000], [15.6000000000, 13], [14.8000000000, 13], [14.8000000000, 14], [0.8000000000, 14], [0.8000000000, 13], [0, 13], [0, 9.5000000000], [0.8000000000, 9.5000000000], [0.8000000000, 4.5000000000], [0, 4.5000000000], [0, 1], [0.8000000000, 1]]);
										}
									}
									translate(v = [38.1000000000, -33.1000000000]) {
										translate(v = [-7.8000000000, -7.0000000000]) {
											polygon(paths = [[0, 1, 2, 3, 4, 5, 6, 7, 8, 9, 10, 11, 12, 13, 14, 15, 16, 17, 18, 19]], points = [[0.8000000000, 0], [14.8000000000, 0], [14.8000000000, 1], [15.6000000000, 1], [15.6000000000, 4.5000000000], [14.8000000000, 4.5000000000], [14.8000000000, 9.5000000000], [15.6000000000, 9.5000000000], [15.6000000000, 13], [14.8000000000, 13], [14.8000000000, 14], [0.8000000000, 14], [0.8000000000, 13], [0, 13], [0, 9.5000000000], [0.8000000000, 9.5000000000], [0.8000000000, 4.5000000000], [0, 4.5000000000], [0, 1], [0.8000000000, 1]]);
										}
									}
									translate(v = [19.0500000000, -38.1000000000]) {
										translate(v = [-7.8000000000, -7.0000000000]) {
											polygon(paths = [[0, 1, 2, 3, 4, 5, 6, 7, 8, 9, 10, 11, 12, 13, 14, 15, 16, 17, 18, 19]], points = [[0.8000000000, 0], [14.8000000000, 0], [14.8000000000, 1], [15.6000000000, 1], [15.6000000000, 4.5000000000], [14.8000000000, 4.5000000000], [14.8000000000, 9.5000000000], [15.6000000000, 9.5000000000], [15.6000000000, 13], [14.8000000000, 13], [14.8000000000, 14], [0.8000000000, 14], [0.8000000000, 13], [0, 13], [0, 9.5000000000], [0.8000000000, 9.5000000000], [0.8000000000, 4.5000000000], [0, 4.5000000000], [0, 1], [0.8000000000, 1]]);
										}
									}
									translate(v = [0.0000000000, -39.1000000000]) {
										translate(v = [-7.8000000000, -7.0000000000]) {
											polygon(paths = [[0, 1, 2, 3, 4, 5, 6, 7, 8, 9, 10, 11, 12, 13, 14, 15, 16, 17, 18, 19]], points = [[0.8000000000, 0], [14.8000000000, 0], [14.8000000000, 1], [15.6000000000, 1], [15.6000000000, 4.5000000000], [14.8000000000, 4.5000000000], [14.8000000000, 9.5000000000], [15.6000000000, 9.5000000000], [15.6000000000, 13], [14.8000000000, 13], [14.8000000000, 14], [0.8000000000, 14], [0.8000000000, 13], [0, 13], [0, 9.5000000000], [0.8000000000, 9.5000000000], [0.8000000000, 4.5000000000], [0, 4.5000000000], [0, 1], [0.8000000000, 1]]);
										}
									}
									translate(v = [95.2500000000, -24.0500000000]) {
										translate(v = [-7.8000000000, -7.0000000000]) {
											polygon(paths = [[0, 1, 2, 3, 4, 5, 6, 7, 8, 9, 10, 11, 12, 13, 14, 15, 16, 17, 18, 19]], points = [[0.8000000000, 0], [14.8000000000, 0], [14.8000000000, 1], [15.6000000000, 1], [15.6000000000, 4.5000000000], [14.8000000000, 4.5000000000], [14.8000000000, 9.5000000000], [15.6000000000, 9.5000000000], [15.6000000000, 13], [14.8000000000, 13], [14.8000000000, 14], [0.8000000000, 14], [0.8000000000, 13], [0, 13], [0, 9.5000000000], [0.8000000000, 9.5000000000], [0.8000000000, 4.5000000000], [0, 4.5000000000], [0, 1], [0.8000000000, 1]]);
										}
									}
									translate(v = [76.2000000000, -23.0500000000]) {
										translate(v = [-7.8000000000, -7.0000000000]) {
											polygon(paths = [[0, 1, 2, 3, 4, 5, 6, 7, 8, 9, 10, 11, 12, 13, 14, 15, 16, 17, 18, 19]], points = [[0.8000000000, 0], [14.8000000000, 0], [14.8000000000, 1], [15.6000000000, 1], [15.6000000000, 4.5000000000], [14.8000000000, 4.5000000000], [14.8000000000, 9.5000000000], [15.6000000000, 9.5000000000], [15.6000000000, 13], [14.8000000000, 13], [14.8000000000, 14], [0.8000000000, 14], [0.8000000000, 13], [0, 13], [0, 9.5000000000], [0.8000000000, 9.5000000000], [0.8000000000, 4.5000000000], [0, 4.5000000000], [0, 1], [0.8000000000, 1]]);
										}
									}
									translate(v = [57.1500000000, -18.0500000000]) {
										translate(v = [-7.8000000000, -7.0000000000]) {
											polygon(paths = [[0, 1, 2, 3, 4, 5, 6, 7, 8, 9, 10, 11, 12, 13, 14, 15, 16, 17, 18, 19]], points = [[0.8000000000, 0], [14.8000000000, 0], [14.8000000000, 1], [15.6000000000, 1], [15.6000000000, 4.5000000000], [14.8000000000, 4.5000000000], [14.8000000000, 9.5000000000], [15.6000000000, 9.5000000000], [15.6000000000, 13], [14.8000000000, 13], [14.8000000000, 14], [0.8000000000, 14], [0.8000000000, 13], [0, 13], [0, 9.5000000000], [0.8000000000, 9.5000000000], [0.8000000000, 4.5000000000], [0, 4.5000000000], [0, 1], [0.8000000000, 1]]);
										}
									}
									translate(v = [38.1000000000, -14.0500000000]) {
										translate(v = [-7.8000000000, -7.0000000000]) {
											polygon(paths = [[0, 1, 2, 3, 4, 5, 6, 7, 8, 9, 10, 11, 12, 13, 14, 15, 16, 17, 18, 19]], points = [[0.8000000000, 0], [14.8000000000, 0], [14.8000000000, 1], [15.6000000000, 1], [15.6000000000, 4.5000000000], [14.8000000000, 4.5000000000], [14.8000000000, 9.5000000000], [15.6000000000, 9.5000000000], [15.6000000000, 13], [14.8000000000, 13], [14.8000000000, 14], [0.8000000000, 14], [0.8000000000, 13], [0, 13], [0, 9.5000000000], [0.8000000000, 9.5000000000], [0.8000000000, 4.5000000000], [0, 4.5000000000], [0, 1], [0.8000000000, 1]]);
										}
									}
									translate(v = [19.0500000000, -19.0500000000]) {
										translate(v = [-7.8000000000, -7.0000000000]) {
											polygon(paths = [[0, 1, 2, 3, 4, 5, 6, 7, 8, 9, 10, 11, 12, 13, 14, 15, 16, 17, 18, 19]], points = [[0.8000000000, 0], [14.8000000000, 0], [14.8000000000, 1], [15.6000000000, 1], [15.6000000000, 4.5000000000], [14.8000000000, 4.5000000000], [14.8000000000, 9.5000000000], [15.6000000000, 9.5000000000], [15.6000000000, 13], [14.8000000000, 13], [14.8000000000, 14], [0.8000000000, 14], [0.8000000000, 13], [0, 13], [0, 9.5000000000], [0.8000000000, 9.5000000000], [0.8000000000, 4.5000000000], [0, 4.5000000000], [0, 1], [0.8000000000, 1]]);
										}
									}
									translate(v = [0.0000000000, -20.0500000000]) {
										translate(v = [-7.8000000000, -7.0000000000]) {
											polygon(paths = [[0, 1, 2, 3, 4, 5, 6, 7, 8, 9, 10, 11, 12, 13, 14, 15, 16, 17, 18, 19]], points = [[0.8000000000, 0], [14.8000000000, 0], [14.8000000000, 1], [15.6000000000, 1], [15.6000000000, 4.5000000000], [14.8000000000, 4.5000000000], [14.8000000000, 9.5000000000], [15.6000000000, 9.5000000000], [15.6000000000, 13], [14.8000000000, 13], [14.8000000000, 14], [0.8000000000, 14], [0.8000000000, 13], [0, 13], [0, 9.5000000000], [0.8000000000, 9.5000000000], [0.8000000000, 4.5000000000], [0, 4.5000000000], [0, 1], [0.8000000000, 1]]);
										}
									}
									translate(v = [95.2500000000, -5.0000000000]) {
										translate(v = [-7.8000000000, -7.0000000000]) {
											polygon(paths = [[0, 1, 2, 3, 4, 5, 6, 7, 8, 9, 10, 11, 12, 13, 14, 15, 16, 17, 18, 19]], points = [[0.8000000000, 0], [14.8000000000, 0], [14.8000000000, 1], [15.6000000000, 1], [15.6000000000, 4.5000000000], [14.8000000000, 4.5000000000], [14.8000000000, 9.5000000000], [15.6000000000, 9.5000000000], [15.6000000000, 13], [14.8000000000, 13], [14.8000000000, 14], [0.8000000000, 14], [0.8000000000, 13], [0, 13], [0, 9.5000000000], [0.8000000000, 9.5000000000], [0.8000000000, 4.5000000000], [0, 4.5000000000], [0, 1], [0.8000000000, 1]]);
										}
									}
									translate(v = [76.2000000000, -4.0000000000]) {
										translate(v = [-7.8000000000, -7.0000000000]) {
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
